nickleassdimebutt/usbc-i2c/output/docs/hierarchical/schematic_block_header.png

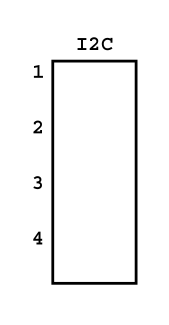
output/docs/hierarchical/schematic_block_header.png
