nickleassdimebutt/usbc-i2c/output/docs/hierarchical/schematic_block_i2c_pullups.png

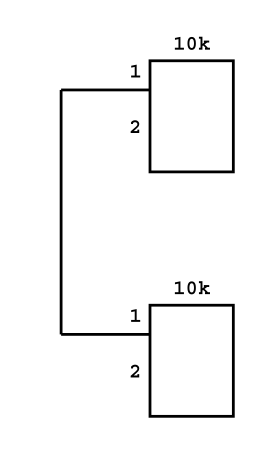
output/docs/hierarchical/schematic_block_i2c_pullups.png
