nickleassdimebutt/usbc-i2c/output/docs/hierarchical/schematic_block_ldo.png

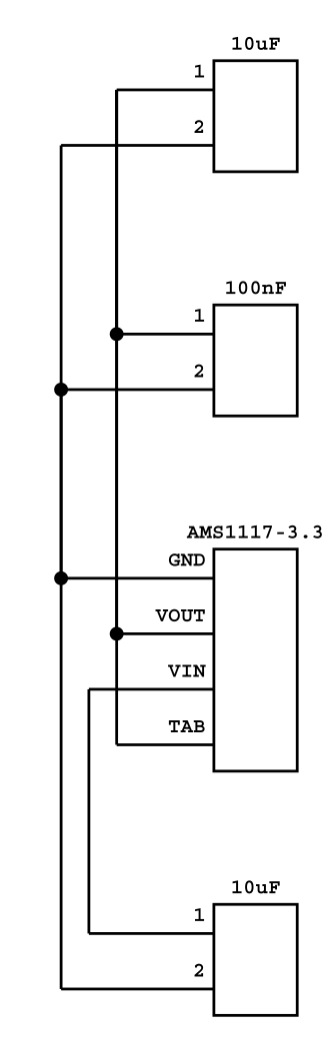
output/docs/hierarchical/schematic_block_ldo.png
