nickleassdimebutt/usbc-i2c/output/docs/hierarchical/schematic_block_led.png

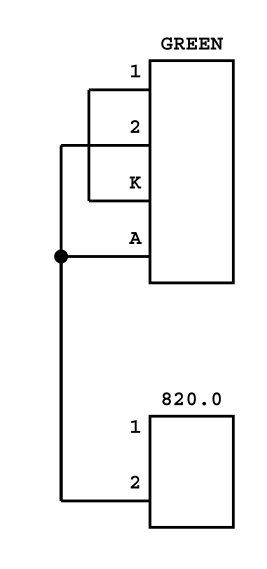
output/docs/hierarchical/schematic_block_led.png
