nickleassdimebutt/usbc-i2c/output/docs/hierarchical/schematic_block_usbc_power.png

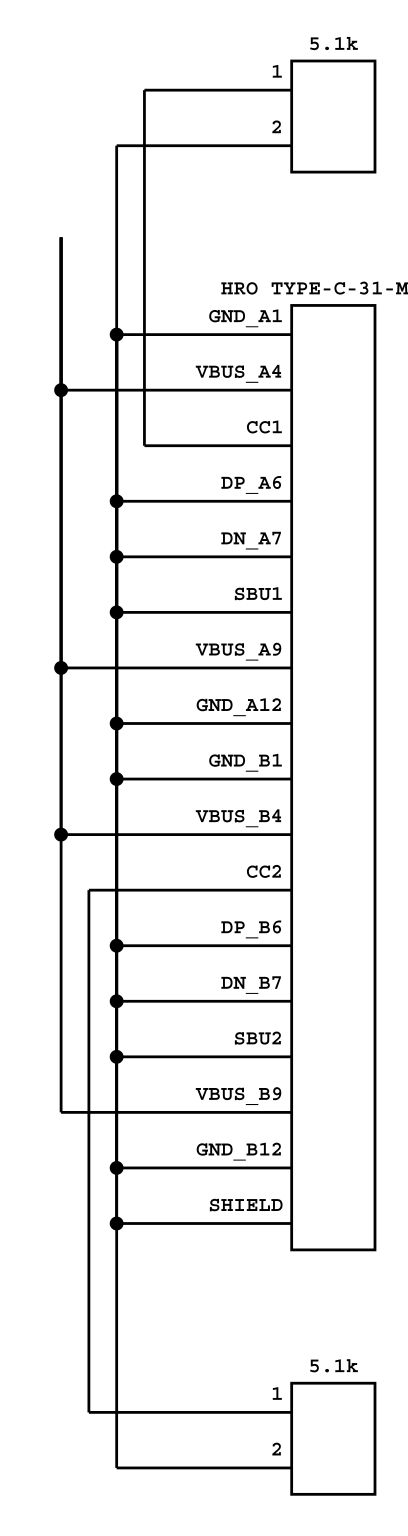
output/docs/hierarchical/schematic_block_usbc_power.png
