nickleassdimebutt/usbc-i2c/output/docs/hierarchical/schematic_overview.png

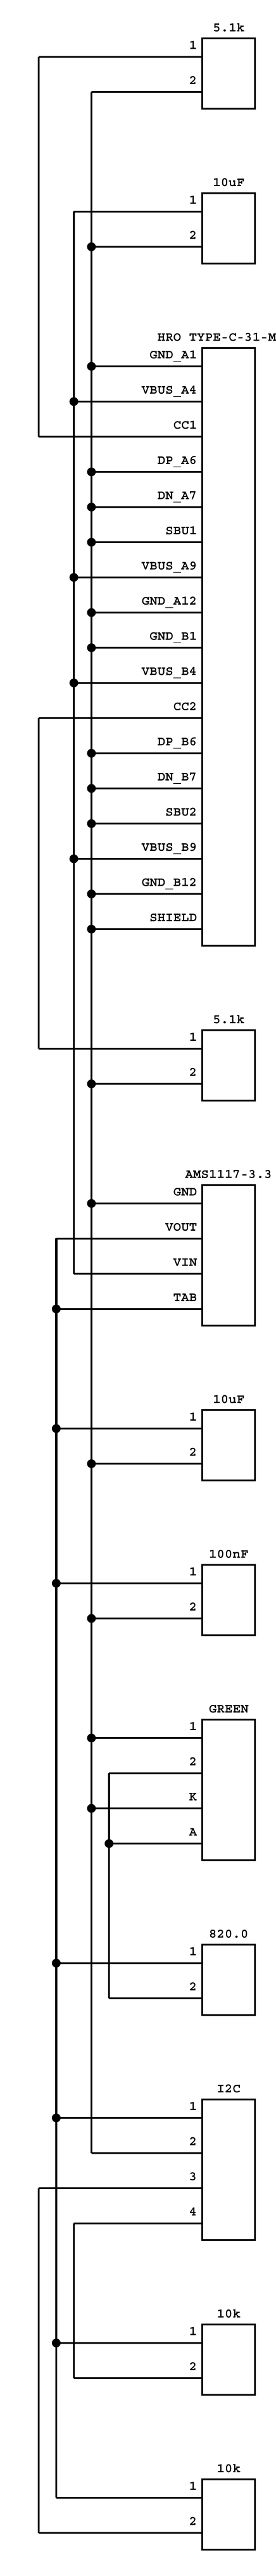
output/docs/hierarchical/schematic_overview.png
