nickleassdimebutt/usbc-i2c/output/render/pcbdraw_back.png

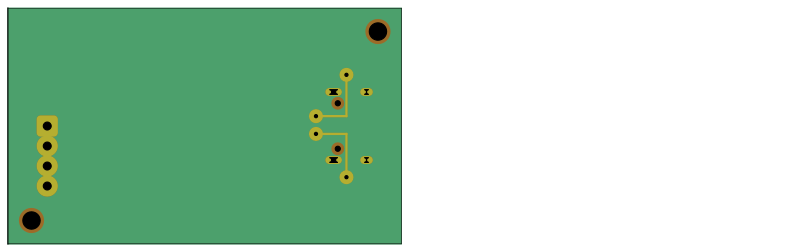
output/render/pcbdraw_back.png
