nickleassdimebutt/usbc-i2c/output/render/pcbdraw_front.png

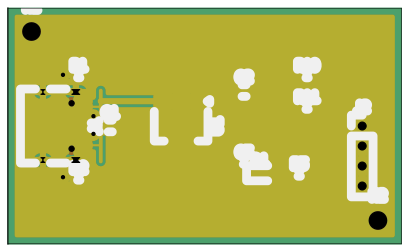
output/render/pcbdraw_front.png
