nickleassdimebutt/usbc-i2c/output/render/render_bottom.png

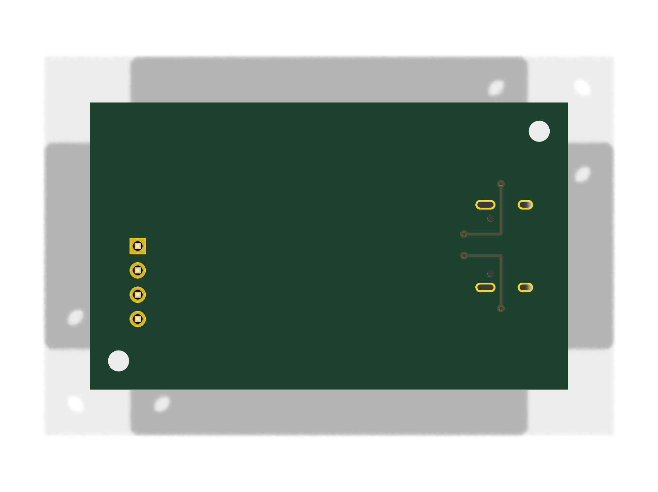
output/render/render_bottom.png
