nickleassdimebutt/usbc-i2c/output/render/render_top.png

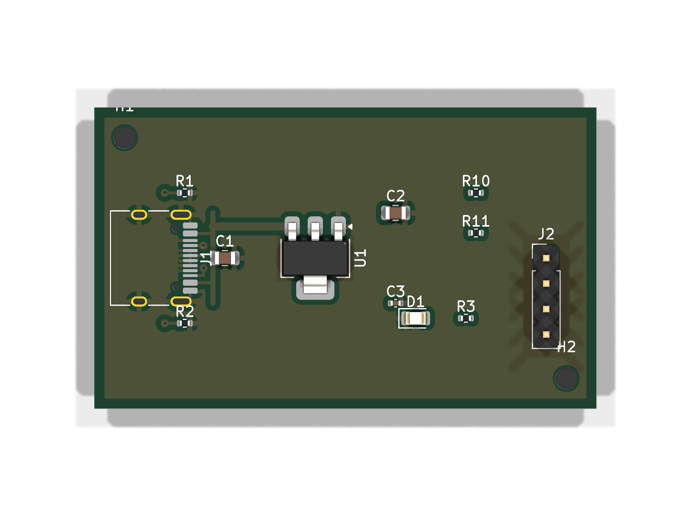
output/render/render_top.png
