nickleassdimebutt/usbc-i2c/output/sim/line_reg.png

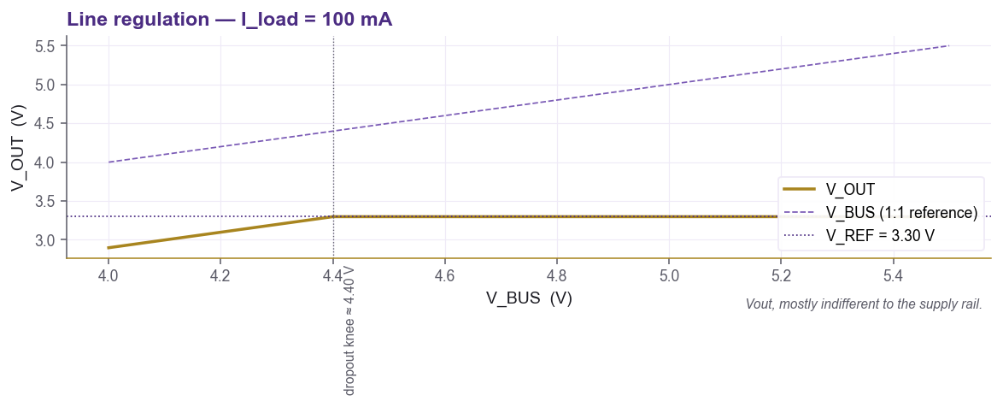
output/sim/line_reg.png
