nickleassdimebutt/usbc-i2c/output/sim/load_reg.png

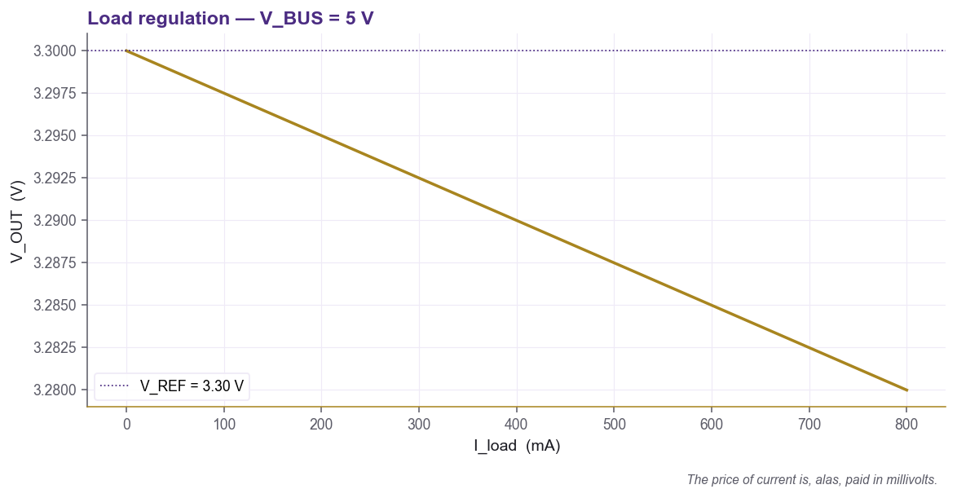
output/sim/load_reg.png
