nickleassdimebutt/usbc-i2c/output/sim/monte_carlo.png

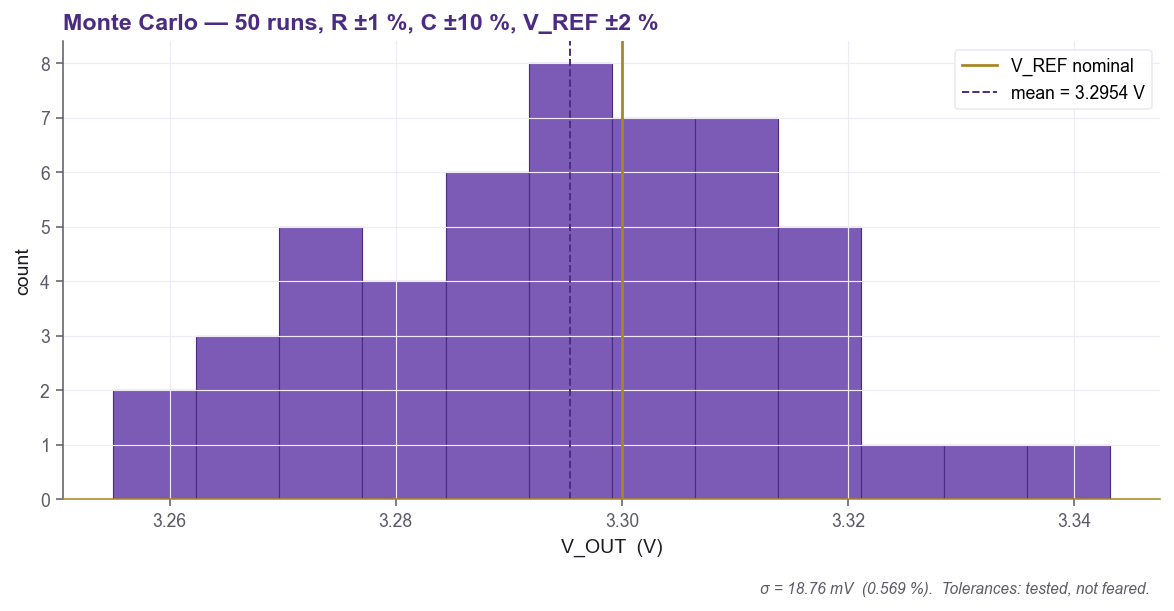
output/sim/monte_carlo.png
