nickleassdimebutt/usbc-i2c/output/sim/temp_sweep.png

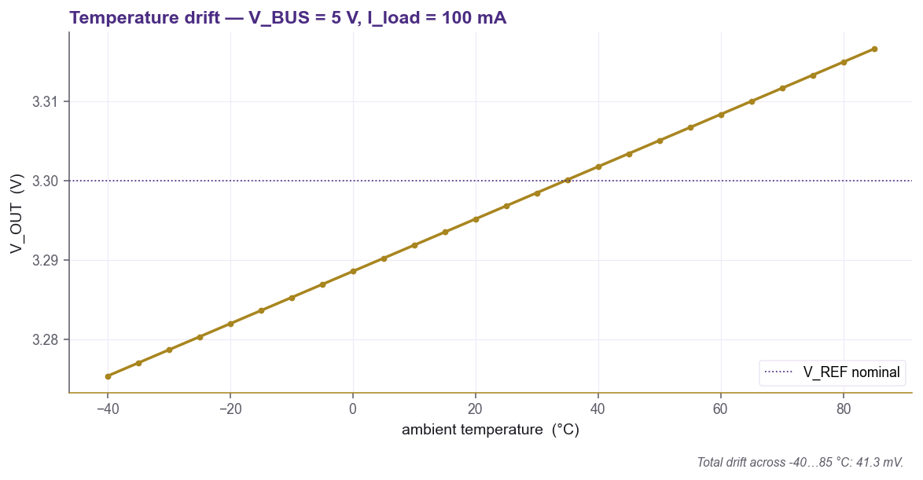
output/sim/temp_sweep.png
