nickleassdimebutt/usbc-i2c/output/sim/transient.png

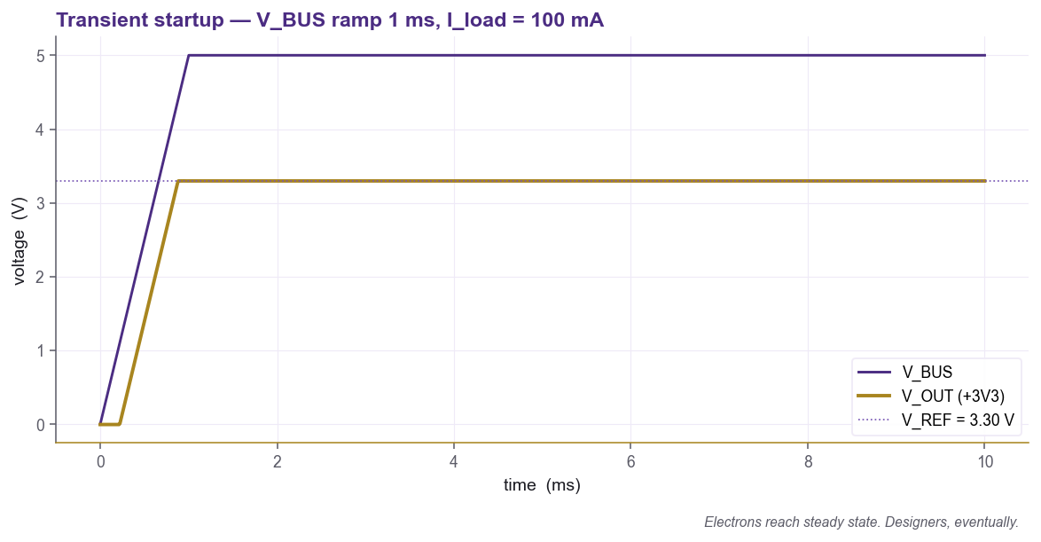
output/sim/transient.png
