nickleassdimebutt/usbc-i2c/output/sim/load_step.png

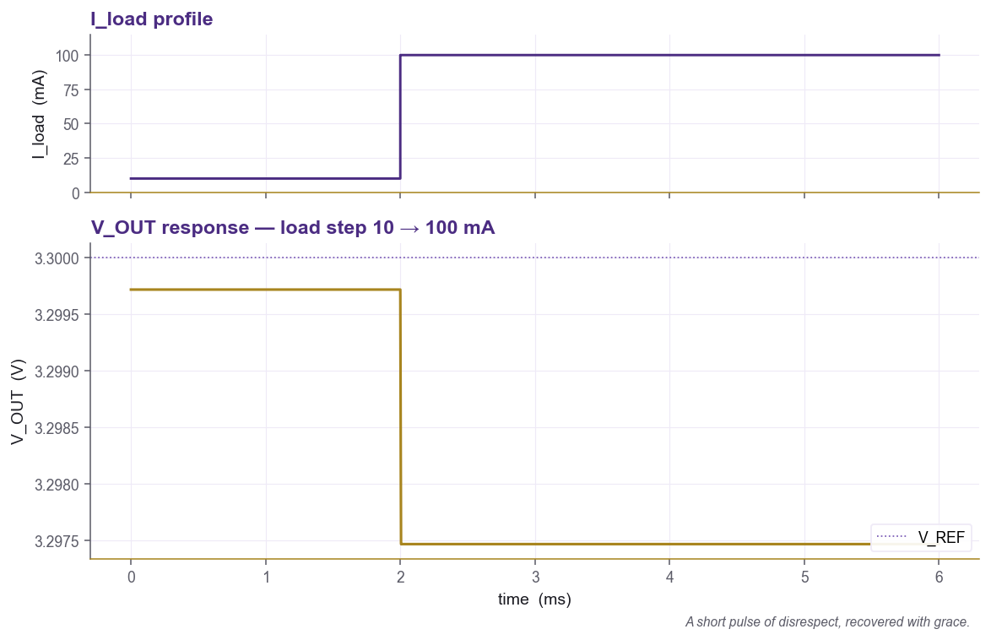
output/sim/load_step.png
